Fifty-Nine/wavegen/hardware/rev3/ltspice/output_amp.asc

C1: cap; 0.8p
C2: cap; 0.8p
C3: cap; 1µ
C4: cap; 2.7p
C5: cap; 4.7µ
C6: cap; 2.7p
C7: cap; 100µ
I1: current; SINE(0.002065 0.002065 {freq} 0 0 0); AC 0.002065 0
I2: current; SINE(0.002065 0.002065 {freq} 0 0 180); AC 0.002065 180
R1: res; {rfdiff}
R2: res; 100
R3: res; 1k
R4: res; 100
R5: res; 1k
R6: res; 1.5k
R7: res; {rfdiff}
R8: res; 100
R9: res; 100
R10: res; 1.5k
R11: res; 36k
R12: res; 36k
R13: res; 50
R14: res; 50
R15: res; 18k
U1: LTC6409
U2: LTC6269
U3: LTC6269
V1: voltage; 3.3
V2: voltage; 3.3
Named nets: InP, InN, 0, OUT-, OUT+, OUT
;.step dec param freq 1meg 100meg 1
;.ac dec 10 1k 200meg
.tran 5000n
.param freq = 10meg
;.op
.param rfdiff 510
