Fifty-Nine/wavegen/software/wavegen/ft2232h-spi.h

/* ft2232h-spi.h
 * Copyright (C) 2017 Tim Prince
 *
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
 * You should have received a copy of the GNU General Public License
 * along with this program.  If not, see <http://www.gnu.org/licenses/>.
 */
#ifndef WAVEGEN_FT2232H_SPI_H
#define WAVEGEN_FT2232H_SPI_H

#include <memory>
#include <vector>

#include "wavegen/exceptions.h"
#include "wavegen/util.h"

namespace wavegen
{

struct packet;

namespace ftdi {

struct error : public wavegen::error
{
public:
    error(const std::string& what) : wavegen::error(what) { }
};

struct endpoint
{
    int vid;
    int pid;
    std::string manufacturer;
    std::string description;
    std::string serial;

    endpoint() = default;
    endpoint(const endpoint&) = default;
    endpoint(endpoint&&) = default;
    endpoint(
        int vid, int pid,
        const std::string& manufacturer,
        const std::string& description,
        const std::string& serial) :
            vid(vid),
            pid(pid),
            manufacturer(manufacturer),
            description(description),
            serial(serial)
    { }

    bool match(const endpoint& other) const {
        return equal_or_defaulted(vid, other.vid) &&
            equal_or_defaulted(pid, other.pid) &&
            equal_or_defaulted(manufacturer, other.manufacturer) &&
            equal_or_defaulted(description, other.description) &&
            equal_or_defaulted(serial, other.serial);
    }
};

std::vector<endpoint> getAvailableEndpoints(int vid, int pid);

struct spi
{
public:
    enum pins : uint8_t {
        adbus0 = 0x01,
        adbus1 = 0x02,
        adbus2 = 0x04,
        adbus3 = 0x08,
        adbus4 = 0x10,
        adbus5 = 0x20,
        adbus6 = 0x40,
        adbus7 = 0x80,

        sck = adbus0,
        sdata = adbus1
    };

    virtual ~spi() noexcept(true);

    spi(pins cs_pin, const endpoint& ep);
    spi(const spi&) = delete;
    spi(spi&&) noexcept(true);

    spi& operator=(const spi&) = delete;
    spi& operator=(spi&&) noexcept(true);

    void transmit(const packet& p);

private:
    enum class opcodes : uint8_t {
        write                = 0x10,
        set_low_bits         = 0x80,
        set_high_bits        = 0x82,
        loopback_enable      = 0x84,
        loopback_disable     = 0x85,
        set_clkdiv           = 0x86,
        clkdiv_5_disable     = 0x8a,
        clkdiv_5_enable      = 0x8b,
        three_phase_enable   = 0x8c,
        three_phase_disable  = 0x8d,
        adaptive_clk_enable  = 0x96,
        adaptive_clk_disable = 0x97,
        bogus                = 0xab
    };


    struct impl;
    std::unique_ptr<impl> d;
};

} /* namespace ftdi */

} /* namespace wavegen */

#endif /* WAVEGEN_FT2232H_SPI_H */
